lingex/IRRemote/V1.2/src/icons.h

#include <Arduino.h>
#include <string>

const unsigned char wifi_icon8x8[] =
{
	0b00111100,
	0b01000010,
	0b10000001,
	0b00011000,
	0b00100100,
	0b00000000,
	0b00000000,
	0b00011000,
};

const unsigned char usb_icon8x8[] =
{
	0b00010000,
	0b00010011,
	0b10010010,
	0b10010100,
	0b01011000,
	0b00110000,
	0b00010000,
	0b00111000,
};
const unsigned char bat0_icon8x8[] =
{
	0b00111100,
	0b01000010,
	0b01000010,
	0b01000010,
	0b01000010,
	0b01000010,
	0b01000010,
	0b01111110,
};
const unsigned char bat1_icon8x8[] =
{
	0b00111100,
	0b01000010,
	0b01000010,
	0b01000010,
	0b01000010,
	0b01000010,
	0b01111110,
	0b01111110,
};
const unsigned char bat2_icon8x8[] =
{
	0b00111100,
	0b01000010,
	0b01000010,
	0b01000010,
	0b01000010,
	0b01111110,
	0b01111110,
	0b01111110,
};
const unsigned char bat3_icon8x8[] =
{
	0b00111100,
	0b01000010,
	0b01000010,
	0b01000010,
	0b01111110,
	0b01111110,
	0b01111110,
	0b01111110,
};
const unsigned char bat4_icon8x8[] =
{
	0b00111100,
	0b01000010,
	0b01000010,
	0b01111110,
	0b01111110,
	0b01111110,
	0b01111110,
	0b01111110,
};
const unsigned char bat5_icon8x8[] =
{
	0b00111100,
	0b01000010,
	0b01111110,
	0b01111110,
	0b01111110,
	0b01111110,
	0b01111110,
	0b01111110,
};
const unsigned char bat6_icon8x8[] =
{
	0b00111100,
	0b01111110,
	0b01111110,
	0b01111110,
	0b01111110,
	0b01111110,
	0b01111110,
	0b01111110,
};
//charge
const unsigned char batc_icon8x8[] =
{
	0b00111100,
	0b01001010,
	0b01010010,
	0b01111110,
	0b01001010,
	0b01010010,
	0b01100010,
	0b01111110,
};


const unsigned char wifi_icon16x8[] =
{
	0b00000111,0b11100000,
	0b00111000,0b00011100,
	0b01100000,0b00000110,
	0b00000011,0b11000000,
	0b00000110,0b01100000,
	0b00000000,0b00000000,
	0b00000001,0b10000000,
	0b00000001,0b10000000,
};

const unsigned char usb_icon16x8[] =
{
	0b00000001,0b11100000,
	0b00000010,0b00000000,
	0b00000100,0b00000000,
	0b11111111,0b11111111,
	0b11000001,0b00000000,
	0b00000000,0b10000000,
	0b00000000,0b01111100,
	0b00000000,0b00000000,
};

const unsigned char bat0_icon16x8[] =
{
	0b00000000,0b00000000,
	0b11111111,0b11111100,
	0b10000000,0b00000010,
	0b10000000,0b00000001,
	0b10000000,0b00000001,
	0b10000000,0b00000001,
	0b10000000,0b00000010,
	0b11111111,0b11111100,
};

const unsigned char bat1_icon16x8[] =
{
	0b00000000,0b00000000,
	0b11111111,0b11111100,
	0b10000000,0b00000010,
	0b10110000,0b00000001,
	0b10110000,0b00000001,
	0b10110000,0b00000001,
	0b10000000,0b00000010,
	0b11111111,0b11111100,
};
const unsigned char bat2_icon16x8[] =
{
	0b00000000,0b00000000,
	0b11111111,0b11111100,
	0b10000000,0b00000010,
	0b10110110,0b00000001,
	0b10110110,0b00000001,
	0b10110110,0b00000001,
	0b10000000,0b00000010,
	0b11111111,0b11111100,
};
const unsigned char bat3_icon16x8[] =
{
	0b00000000,0b00000000,
	0b11111111,0b11111100,
	0b10000000,0b00000010,
	0b10110110,0b11000001,
	0b10110110,0b11000001,
	0b10110110,0b11000001,
	0b10000000,0b00000010,
	0b11111111,0b11111100,
};
const unsigned char bat4_icon16x8[] =
{
	0b00000000,0b00000000,
	0b11111111,0b11111100,
	0b10000000,0b00000010,
	0b10110110,0b11011001,
	0b10110110,0b11011001,
	0b10110110,0b11011001,
	0b10000000,0b00000010,
	0b11111111,0b11111100,
};

//base64 icon
String favicon = "AAABAAEAICAAAAEAIAAoEAAAFgAAACgAAAAgAAAAQAAAAAEAIAAAAAAAABAAAAAAAAAAAAAAAAAAAAAAAAAAAAAAAAAAAAAAAAAAAAAAAAAAAAAAAAAAAAAAAAAAFQAAA\
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
